ipleiria-robotics/iModDom/1_Documentacao/2_Hardware/09_Shunt_Board_V2.0/README.md

# iModDom
## *Shunt Board V2.0*
- Esta versão já foi fabricada e testada, pelo que se encontra totalmente funcional.
