ipleiria-robotics/iModDom/1_Documentacao/2_Hardware/08_Remote_Board_V2.0/README.md

# iModDom
## *Remote Board V2.0*
- Esta versão está finalizada, no entanto, à presente data não foi fabricada nem testada, pelo que a sua utilização fica à responsabilidade do utilizador.
- Esta versão conta com as seguintes melhorias:

    1.Melhoria a nível do legendamento dos componentes, com realce na legenda da porta RJ45.
    
    2.*Solder jumper* em alternativa à resistência.
