ipleiria-robotics/iModDom/1_Documentacao/2_Hardware/07_Main_Board_V2.0/README.md

# iModDom
## *Main Board V2.0*
- Esta versão está finalizada, no entanto, à presente data não foi fabricada nem testada, pelo que a sua utilização fica à responsabilidade do utilizador.
- Esta versão conta com as seguintes melhorias:

    1.Melhoria a nível do legendamento dos componentes, com realce na legenda do módulo de portas RJ45.
    
    3.Furação de fixação da placa.
    
    4.*Solder jumper* em alternativa à resistência.
