ipleiria-robotics/iModDom/1_Documentacao/2_Hardware/02_Eagle_Libraries/README.md

# iModDom
## Bibliotecas
- Aqui estão disponíveis todoas as bibliotecas utilizadas para o desenvolvimento das placas de circuito impresso do projeto.
