ipleiria-robotics/iModDom/1_Documentacao/2_Hardware/01_Lista_de_Hardware/README.md

# iModDom
## *Lista de Hardware*
- Nesta pasta pode verificar os custos do projeto de forma descriminada. Note que podem existir variações nos valores.
