ipleiria-robotics/iModDom/1_Documentacao/2_Hardware/03_Main_Board_V1.0/README.md

# iModDom
## *Main Board V1.0*
- Esta versão já foi fabricada e testada, pelo que se encontra totalmente funcional.
