ipleiria-robotics/iModDom/1_Documentacao/2_Hardware/04_Remote_Board_V1.0/README.md

# iModDom
## *Remote Board V1.0*
- Esta versão já foi fabricada e testada, pelo que se encontra totalmente funcional.
